miek770/marcus-bbbcape/media/bbbcape.png

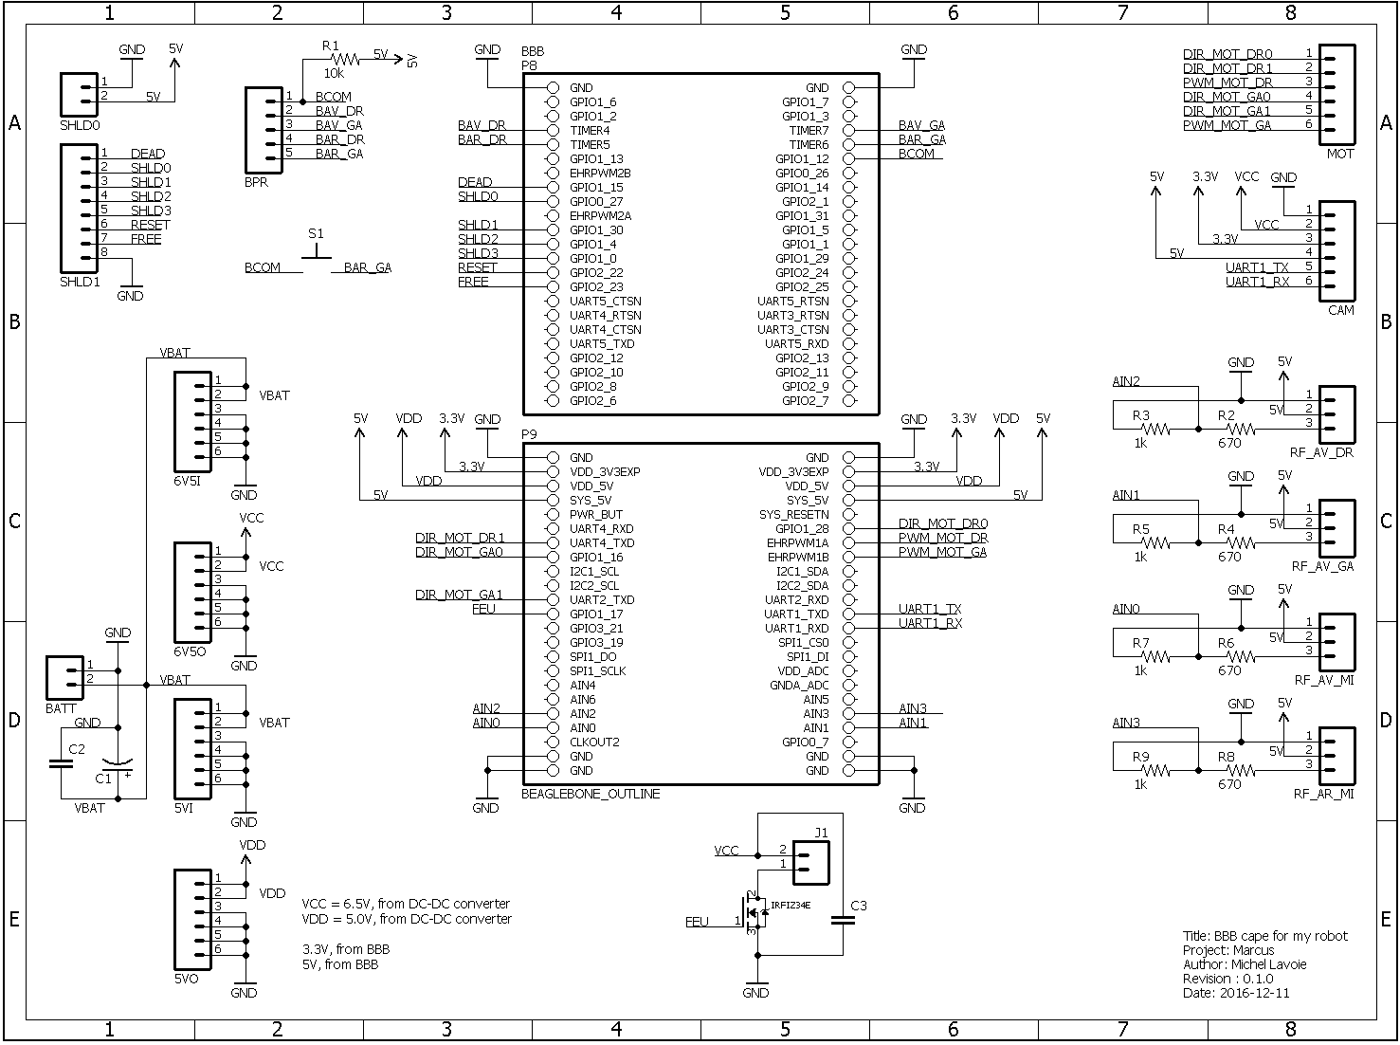
media/bbbcape.png
