miek770/marcus-bbbcape/media/Bottom layer.png

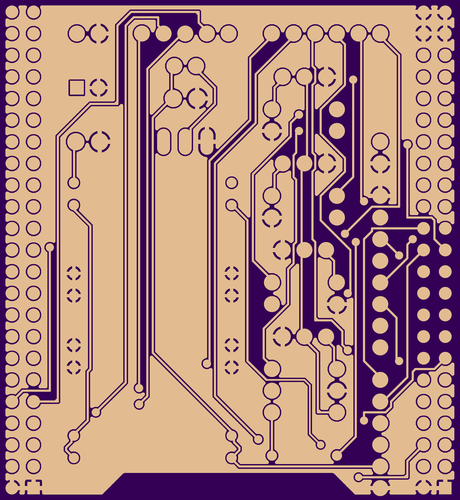
media/Bottom layer.png
